Runningtarrens/Mcorne-c5/pictures/20221026_122507.jpg

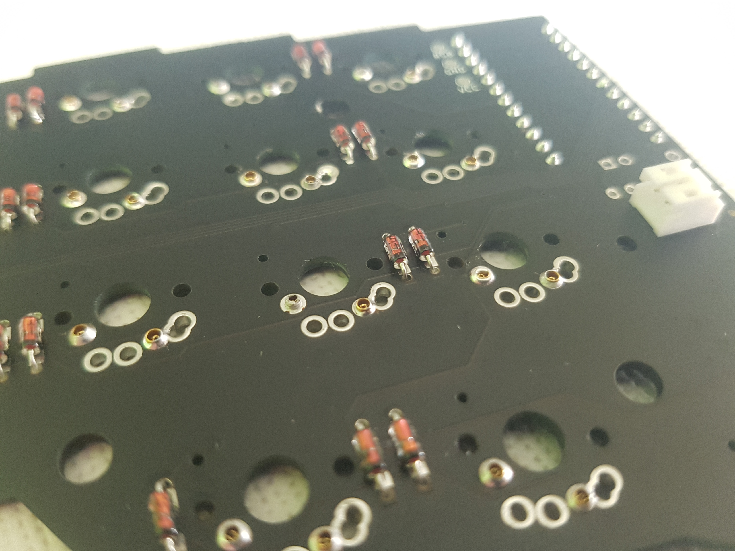
pictures/20221026_122507.jpg
