Runningtarrens/Mcorne-c5/pictures/20221110_092711.jpg

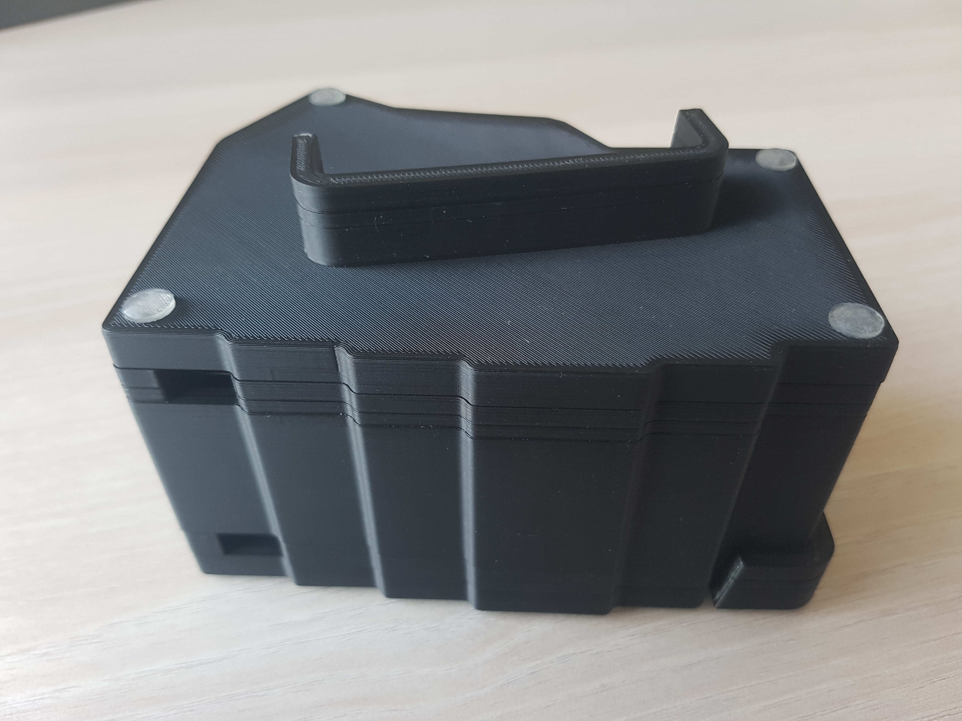
pictures/20221110_092711.jpg
