Runningtarrens/Mcorne-c5/pictures/20221110_092823.jpg

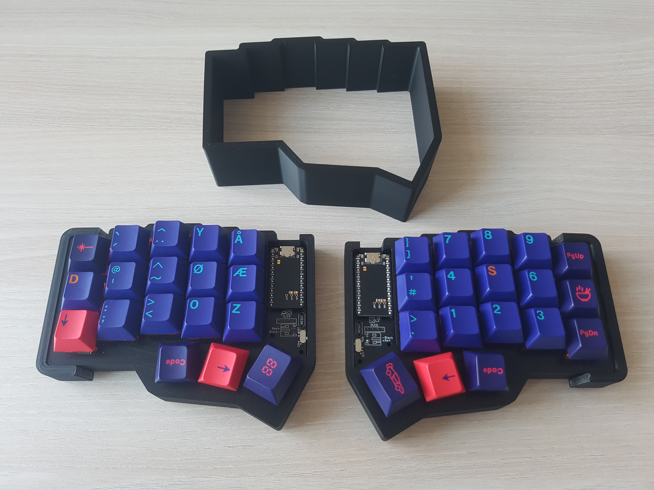
pictures/20221110_092823.jpg
