Runningtarrens/Mcorne-c5/pictures/20221110_092959.jpg

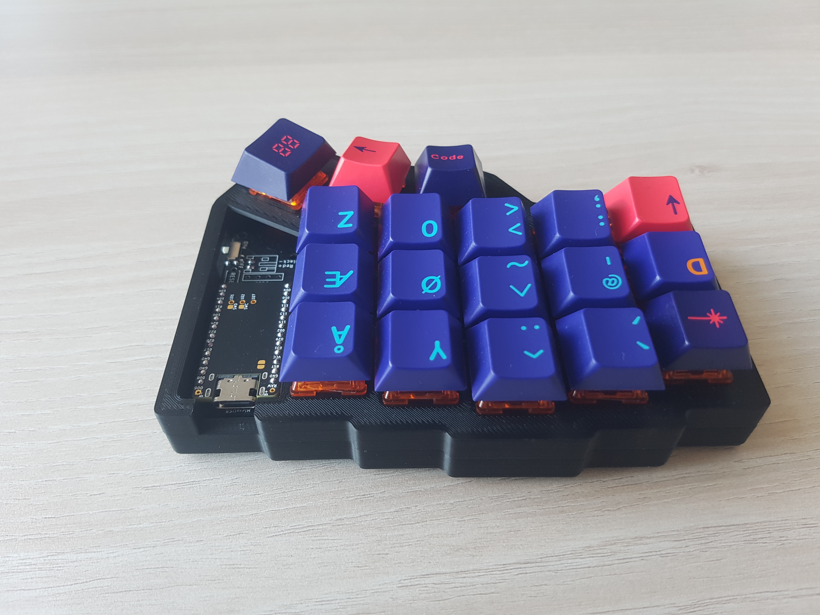
pictures/20221110_092959.jpg
