Runningtarrens/Mcorne-c5/pictures/20221110_093053.jpg

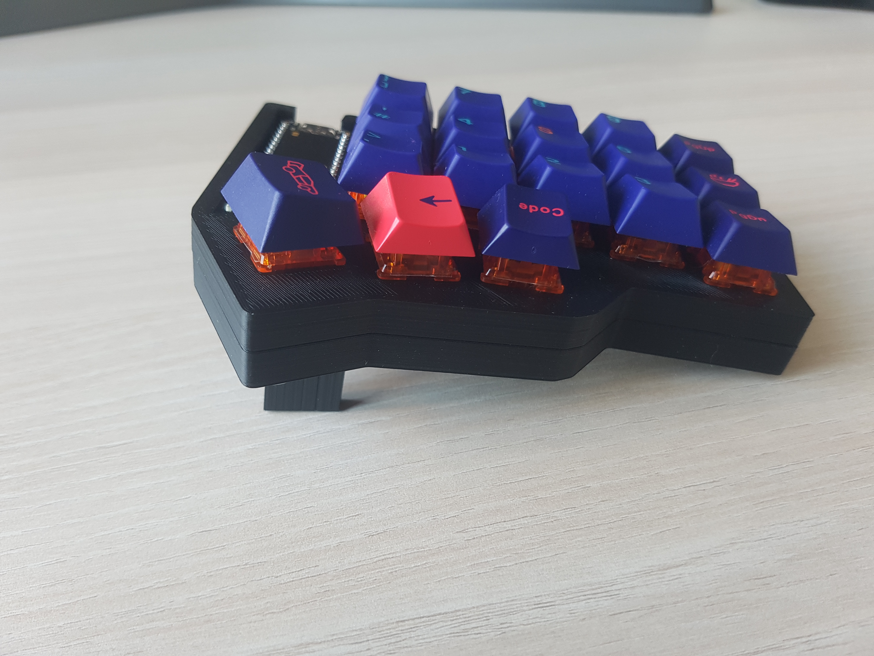
pictures/20221110_093053.jpg
