Runningtarrens/Mcorne-c5/pictures/20221110_093117.jpg

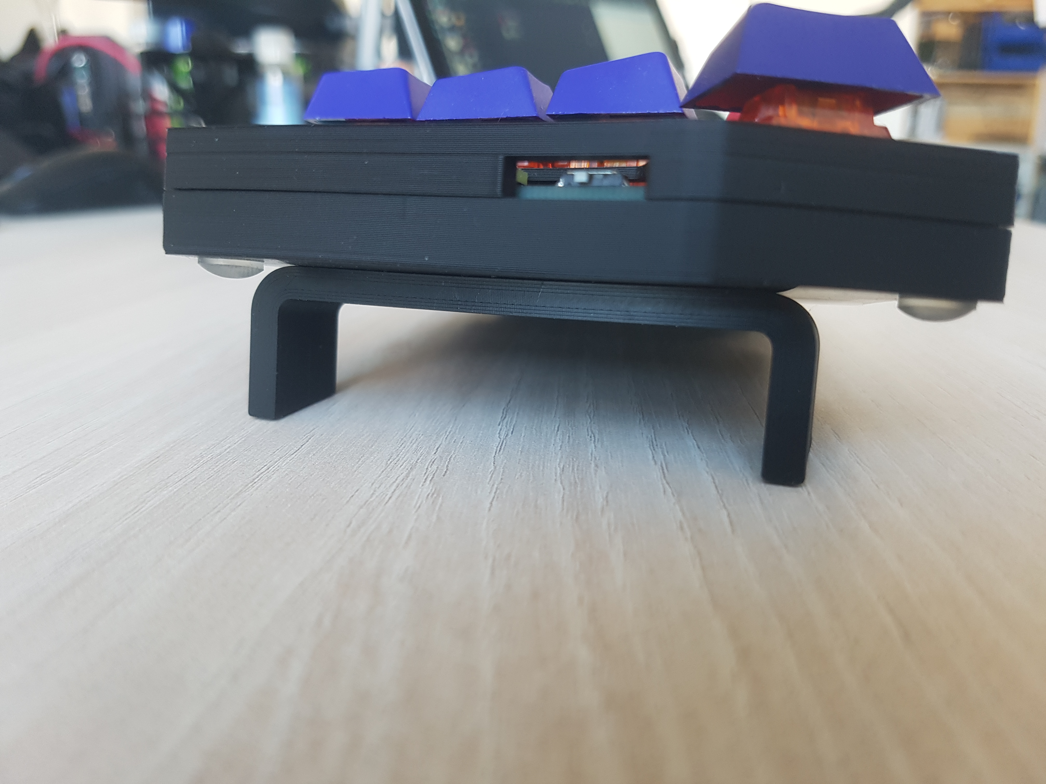
pictures/20221110_093117.jpg
