Runningtarrens/Mcorne-c5/pictures/20221110_093253.jpg

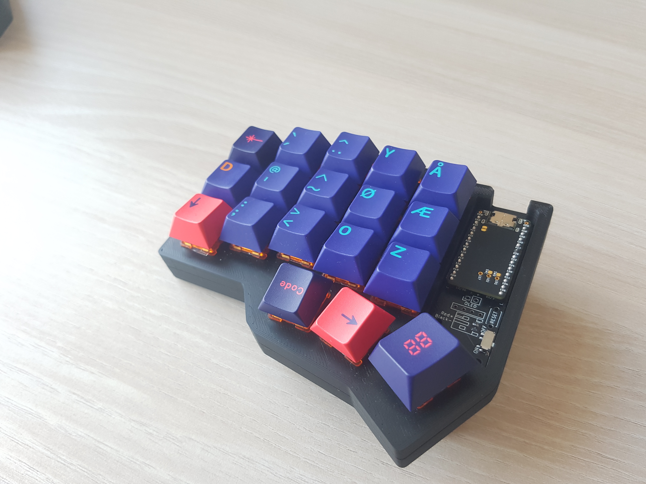
pictures/20221110_093253.jpg
