Runningtarrens/Mcorne-c5/pictures/slice6.JPG

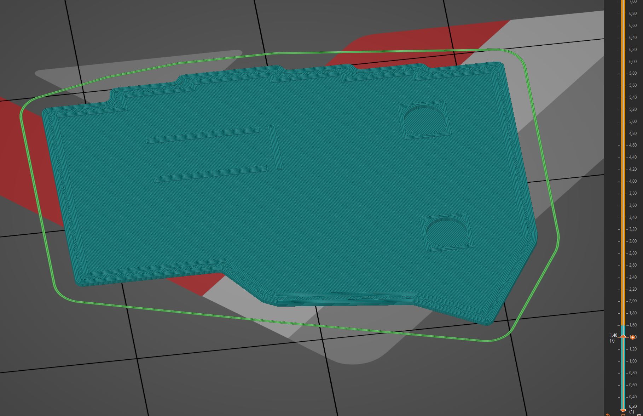
pictures/slice6.JPG
